maybar/DigitalClock/Software/DigitalClock/Credentials_example.h

#ifndef CREDENTIALS_H
#define CREDENTIALS_H

/**
 * Archivo de ejemplo para las credenciales de WiFi
 * 
 * INSTRUCCIONES:
 * 1. Copia este archivo y renómbralo a "Credentials.h" en el mismo directorio
 * 2. Reemplaza "YOUR_SSID" con el nombre de tu red WiFi
 * 3. Reemplaza "YOUR_PASSWORD" con la contraseña de tu red WiFi
 * 4. Guarda el archivo Credentials.h (este archivo debe estar en .gitignore)
 */

// SSID de tu red WiFi
#define SID "YOUR_SSID"

// Contraseña de tu red WiFi
#define PW "YOUR_PASSWORD"

#endif /* CREDENTIALS_H */
